Valar-Systems/MiniSpeedCam/docs/images/back1.jpg

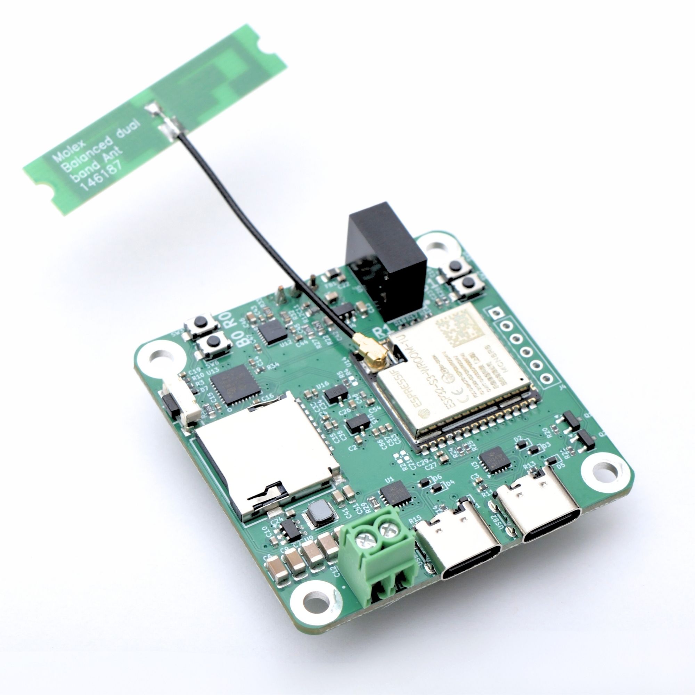
docs/images/back1.jpg
