Valar-Systems/MiniSpeedCam/docs/images/back2.jpg

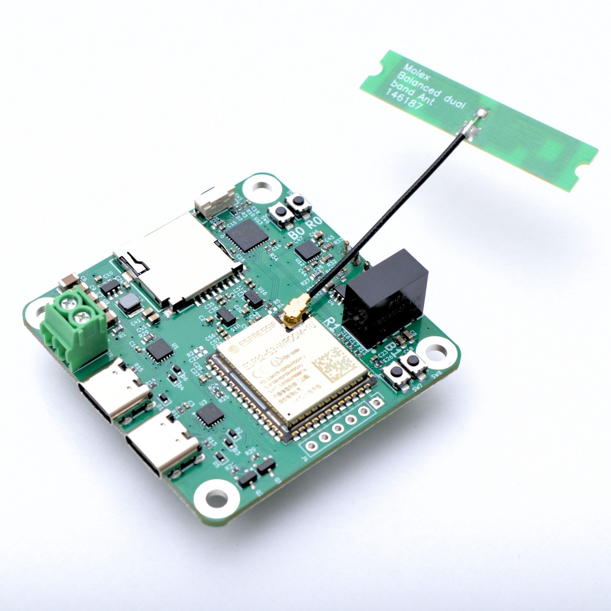
docs/images/back2.jpg
