Valar-Systems/MiniSpeedCam/docs/images/front1.jpg

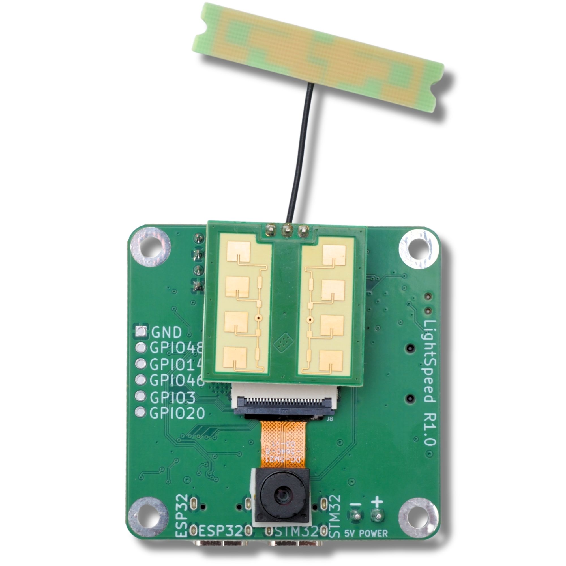
docs/images/front1.jpg
