Valar-Systems/MiniSpeedCam/docs/images/front2.jpg

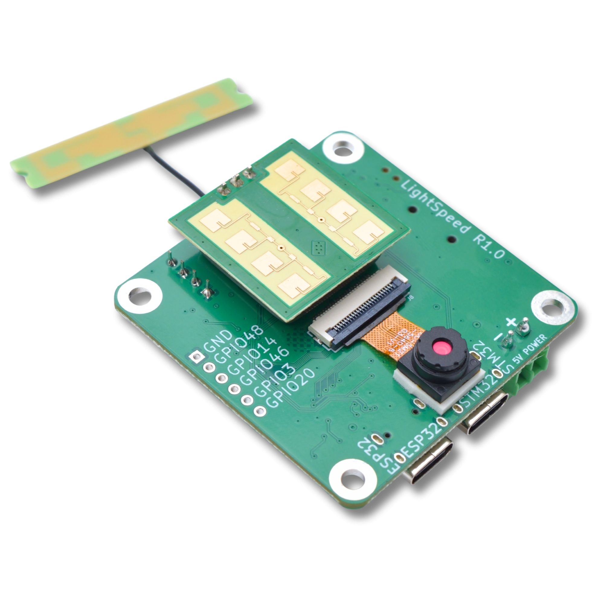
docs/images/front2.jpg
