Valar-Systems/MiniSpeedCam/version/r1.2/firmware/esp32_firmware_1-2/Arduino_Configuration_USB_UART.png

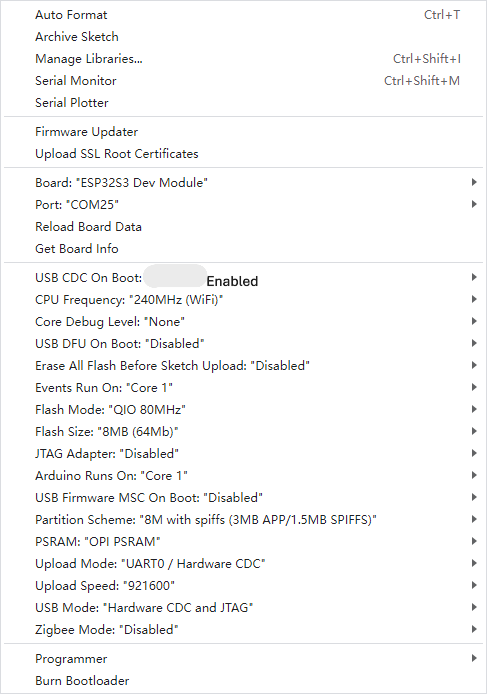
version/r1.2/firmware/esp32_firmware_1-2/Arduino_Configuration_USB_UART.png
