Valar-Systems/MiniSpeedCam/version/r1.1/firmware/platformio/esp32_firmware_platformio/src/config.h

/**
 * config.h - Deployment configuration for the MiniSpeedCam firmware.
 *
 * One firmware image serves every unit; per-deployment values come in through
 * PlatformIO build flags, not committed constants. See platformio.ini
 * `build_flags` and the build-flag note in the repo for the exact values.
 */
#pragma once

// --- Bootstrap bearer token (transport auth only) ---------------------------
// Authorizes the register_device / capture transport. It is NOT a user-data
// key: on its own it can only register a device or post a capture for an
// already-claimed device -- it cannot read or write a user's data. Because the
// previous shared key leaked into this repo's git history, the token is now
// REQUIRED at build time and intentionally has no in-source default:
//   build_flags = '-DAPI_BEARER_TOKEN="<rotated-bootstrap-token>"'
// The build fails loudly below if it is missing, so a unit can never ship with
// a stale/placeholder token baked in.
#ifndef API_BEARER_TOKEN
#error "API_BEARER_TOKEN is not defined. Pass it via a PlatformIO build flag, e.g. build_flags = '-DAPI_BEARER_TOKEN=\"<rotated-bootstrap-token>\"'. It must never be committed in source."
#endif
// Catch an EMPTY token too: an unset '${sysenv.MSC_BOOTSTRAP_TOKEN}' expands to
// "", which the #ifndef above cannot see (the macro is still "defined"). A bare
// "" has sizeof 1 (just the NUL), so this fails the build if no token was set.
static_assert(sizeof(API_BEARER_TOKEN) > 1,
              "API_BEARER_TOKEN is empty -- set MSC_BOOTSTRAP_TOKEN before building (it must not be committed in source).");

// --- Cloud API base URL (Bubble version-test vs version-live) ----------------
// All workflow endpoints in variables.h are built from this base. Defaults to
// the test environment; switch to production with a build flag:
//   build_flags = '-DAPI_BASE_URL="https://minispeedcam.com/version-live/api/1.1/wf"'
#ifndef API_BASE_URL
#define API_BASE_URL "https://minispeedcam.com/version-test/api/1.1/wf"
#endif

// --- TLS trust anchors -------------------------------------------------------
// Roots used by WiFiClientSecure to validate minispeedcam.com instead of the
// old setInsecure() (MITM-vulnerable) behaviour. The live leaf is issued by
// Google Trust Services and rotates ~every 90 days, so we pin the long-lived
// ROOT, not the leaf/intermediate:
//   - GTS Root R4   (current issuer's root)
//   - ISRG Root X1  (Let's Encrypt; a hedge in case the managed cert provider
//                    is ever switched, so OTA can't be bricked fleet-wide)
// setCACert() parses multiple concatenated PEMs, so both are embedded. A CA
// root is public, so committing it is fine -- and embedding (vs a -D flag)
// keeps TLS validation ON by default, since a multi-line PEM does not fit a
// build flag cleanly. Override with -DAPI_CA_ROOT_CERT if you need a different
// anchor; an empty string falls back to setInsecure().
#ifndef API_CA_ROOT_CERT
#define API_CA_ROOT_CERT R"PEM(
-----BEGIN CERTIFICATE-----
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
-----END CERTIFICATE-----
-----BEGIN CERTIFICATE-----
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
-----END CERTIFICATE-----
)PEM"
#endif

static const char* kCaRootCert = API_CA_ROOT_CERT;

// --- GitHub auto-update (firmware now self-updates from GitHub Releases) ------
// Firmware updates no longer go through the manual Bubble "firmware_check" +
// web-UI buttons. Each device polls this PUBLIC repo's Releases for the latest
// tag, reads a manifest.json release asset for the per-MCU versions + .bin URLs
// + MD5s, and auto-applies any STRICTLY NEWER image while idle (see ota.h). The
// repo is public, so no token is embedded. Owner/repo are build-flag overridable
// so a fork can point the fleet at its own releases.
#ifndef GITHUB_OWNER
#define GITHUB_OWNER "Valar-Systems"
#endif
#ifndef GITHUB_REPO
#define GITHUB_REPO "MiniSpeedCam"
#endif

// Cadence. The unauthenticated GitHub API allows 60 requests/hour per IP; a
// multi-hour cadence stays far under that even for several units behind one NAT.
// The first check waits OTA_BOOT_CHECK_DELAY_MS after boot so it never competes
// with start-up / the first WiFi association.
#ifndef OTA_CHECK_INTERVAL_MS
#define OTA_CHECK_INTERVAL_MS (6UL * 60UL * 60UL * 1000UL)  // 6 hours
#endif
#ifndef OTA_BOOT_CHECK_DELAY_MS
#define OTA_BOOT_CHECK_DELAY_MS (2UL * 60UL * 1000UL)       // 2 minutes
#endif

// Health-check window for a freshly-applied ESP image. After applying, the new
// image must reach the cloud once within this window AND within OTA_HEALTH_MAX_BOOTS
// reboots, or the watchdog reverts to the previous slot (see otaHealthService()).
#ifndef OTA_HEALTH_TIMEOUT_MS
#define OTA_HEALTH_TIMEOUT_MS (5UL * 60UL * 1000UL)         // 5 minutes
#endif
#ifndef OTA_HEALTH_MAX_BOOTS
#define OTA_HEALTH_MAX_BOOTS 3                               // reboots before giving up + reverting
#endif

// --- TLS roots for the GitHub update path ------------------------------------
// The whole update path is TLS-authenticated against pinned roots (and the
// binary is additionally MD5-verified as defense-in-depth). GitHub currently
// serves two distinct chains, so the bundle pins the root of each:
//   - USERTrust ECC Certification Authority  -> api.github.com / codeload.github.com
//                                               (release metadata + version discovery)
//   - ISRG Root X1 (Let's Encrypt)           -> *.githubusercontent.com
//                                               (manifest.json + the .bin asset downloads)
//   - DigiCert Global Root G2                -> hedge: GitHub used DigiCert before the
//                                               Sectigo/USERTrust migration and may rotate back
// setCACert() parses multiple concatenated PEMs, and HTTPClient keeps the same
// client (hence the same CA set) across the github.com -> githubusercontent.com
// asset redirect, so one bundle validates every hop. Override with
// -DGITHUB_CA_ROOT_CERT (an empty string makes the GitHub fetch fall back to
// setInsecure(), still MD5-verified).
// NOTE: if GitHub moves to a CA not covered here, auto-update simply STALLS --
// the device keeps running its current firmware (non-bricking). Refresh these
// roots and ship a build. (A signed-manifest scheme would drop the CA dependency
// entirely; a possible future hardening.)
#ifndef GITHUB_CA_ROOT_CERT
#define GITHUB_CA_ROOT_CERT R"PEM(
-----BEGIN CERTIFICATE-----
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
-----END CERTIFICATE-----
-----BEGIN CERTIFICATE-----
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
-----END CERTIFICATE-----
-----BEGIN CERTIFICATE-----
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
MrY=
-----END CERTIFICATE-----
)PEM"
#endif
static const char* kGithubCaRootCert = GITHUB_CA_ROOT_CERT;
