Valar-Systems/MiniSpeedCam/version/r1.1/firmware/platformio/esp32_firmware_platformio/src/camera.h

/**
 * camera.h - OV2640 camera setup and capture for the MiniSpeedCam.
 *
 * The PWDN and RESET lines are wired to dedicated MCU GPIOs
 * (CAMERA_PWDN_PIN / CAMERA_RST_PIN, defined in the main sketch) so
 * the esp_camera config below sets PWDN_GPIO_NUM/RESET_GPIO_NUM to -1
 * and we toggle them manually in cameraPowerOn().
 */

// --- OV2640 to ESP32-S3 pin mapping (board revision 1.1) ---
#define PWDN_GPIO_NUM -1
#define RESET_GPIO_NUM -1
#define XCLK_GPIO_NUM 16
#define SIOD_GPIO_NUM 4
#define SIOC_GPIO_NUM 5

#define Y2_GPIO_NUM 9
#define Y3_GPIO_NUM 11
#define Y4_GPIO_NUM 12
#define Y5_GPIO_NUM 10
#define Y6_GPIO_NUM 13
#define Y7_GPIO_NUM 18
#define Y8_GPIO_NUM 17
#define Y9_GPIO_NUM 15

#define VSYNC_GPIO_NUM 6
#define HREF_GPIO_NUM 7
#define PCLK_GPIO_NUM 8

/**
 * Power-cycle the OV2640.
 *
 * Drives PWDN low (sensor enabled) and pulses RST low->high to bring
 * the sensor out of reset cleanly. Must be called before cameraSetup().
 */
void cameraPowerOn() {
  digitalWrite(CAMERA_PWDN_PIN, LOW);
  digitalWrite(CAMERA_RST_PIN, LOW);
  delay(10);
  digitalWrite(CAMERA_RST_PIN, HIGH);
  delay(10);
}

/**
 * Initialize the OV2640 via esp_camera.
 *
 * Configures pin mapping, 20 MHz XCLK, UXGA (1600x1200) JPEG output
 * stored in PSRAM, and applies sensor tweaks (vflip, brightness).
 *
 * @return 1 on success, 0 if esp_camera_init() failed (see Serial log).
 */
int cameraSetup(void) {
  camera_config_t config = {};  // zero-init so fields we don't set explicitly (e.g. sccb_i2c_port) start at 0, not garbage
  config.ledc_channel = LEDC_CHANNEL_0;
  config.ledc_timer = LEDC_TIMER_0;
  config.pin_d0 = Y2_GPIO_NUM;
  config.pin_d1 = Y3_GPIO_NUM;
  config.pin_d2 = Y4_GPIO_NUM;
  config.pin_d3 = Y5_GPIO_NUM;
  config.pin_d4 = Y6_GPIO_NUM;
  config.pin_d5 = Y7_GPIO_NUM;
  config.pin_d6 = Y8_GPIO_NUM;
  config.pin_d7 = Y9_GPIO_NUM;
  config.pin_xclk = XCLK_GPIO_NUM;
  config.pin_pclk = PCLK_GPIO_NUM;
  config.pin_vsync = VSYNC_GPIO_NUM;
  config.pin_href = HREF_GPIO_NUM;
  config.pin_sccb_sda = SIOD_GPIO_NUM;
  config.pin_sccb_scl = SIOC_GPIO_NUM;
  config.pin_pwdn = PWDN_GPIO_NUM;
  config.pin_reset = RESET_GPIO_NUM;
  config.xclk_freq_hz = 20000000;  // 20 mzh or 16 mhz

  /*
  FRAMESIZE_UXGA (1600 x 1200)
  FRAMESIZE_QVGA (320 x 240)
  FRAMESIZE_CIF (352 x 288)
  FRAMESIZE_VGA (640 x 480)
  FRAMESIZE_SVGA (800 x 600)
  FRAMESIZE_XGA (1024 x 768)
  FRAMESIZE_SXGA (1280 x 1024)
  */

  config.frame_size = FRAMESIZE_UXGA;
  config.pixel_format = PIXFORMAT_JPEG;
  config.grab_mode = CAMERA_GRAB_LATEST;
  config.fb_location = CAMERA_FB_IN_PSRAM;
  config.jpeg_quality = 20; //The image quality (jpeg_quality) can be a number between 0 and 63. Higher is better quality, but causes performance issues
  config.fb_count = 2;  // double-buffer so Core 1 can capture a new frame while Core 0 still streams the previous one

  // camera init
  esp_err_t err = esp_camera_init(&config);
  if (err != ESP_OK) {
    Serial.printf("Camera init failed with error 0x%x", err);
    return 0;
  }

  sensor_t* s = esp_camera_sensor_get();
  // Orientation for the camera as mounted in this enclosure: vflip OFF (it was
  // enabled, which left the image upside down). Colors run a touch saturated,
  // so trim brightness/saturation below. This applies to BOTH the aiming stream
  // and the uploaded speed photos -- they share the one sensor.
  s->set_vflip(s, 0);       // 0 = disable , 1 = enable (flips top<->bottom)
  s->set_hmirror(s, 0);     // 0 = disable , 1 = enable (flips left<->right)
  s->set_brightness(s, 1);  // up the brightness just a bit
  s->set_saturation(s, 0);  // lower the saturation

  Serial.println("Camera configuration complete!");
  return 1;
}

/**
 * Capture a single JPEG frame and return its framebuffer.
 *
 * The framebuffer is NOT released here; the CALLER (taskCore1) must
 * esp_camera_fb_return() it. taskCore1 copies the JPEG into a PSRAM buffer and
 * returns the framebuffer immediately, so the driver's fb pool is never held
 * across the slow upload (which would block a subsequent capture). Returns
 * nullptr on capture failure (the run then uploads speed-only).
 */
camera_fb_t* capturePhoto(void) {
  camera_fb_t* fb = esp_camera_fb_get();  // Capture photo
  if (!fb) {
    Serial.println("[CAM] capture FAILED");
    return nullptr;
  }
  Serial.printf("[CAM] captured %u bytes\n", (unsigned)fb->len);
  return fb;
}
