Valar-Systems/MiniSpeedCam/version/r1.2/firmware/esp32_firmware_1-2_platformio/src/espui_settings.h

/**
 * espui_settings.h - ESPUI web UI controls and persistence callbacks.
 *
 * Builds the configuration portal exposed at the device's IP:
 *   - "Device" tab:  speed units toggle, minimum speed, photo speed.
 *   - "Wifi Settings" tab: SSID/password/camera-id text inputs, plus
 *     Save (writes to NVS and reboots) and Clear Settings buttons.
 *
 * Each control's callback updates the matching global in variables.h
 * and persists it via the shared `preferences` (NVS) instance.
 */
#pragma once

/**
 * Build the ESPUI control tree and start serving it.
 */
void load_espui();

/**
 * Refresh the Status-tab labels (current speed, free heap, RSSI, etc.).
 * Throttled internally to ~1 Hz, so it's safe to call every iteration
 * of taskCore0. No-op until load_espui() has run.
 */
void espuiDiagnosticsTick();
